mahaoran1997/vision.github.io/assets/images/Model Base.png

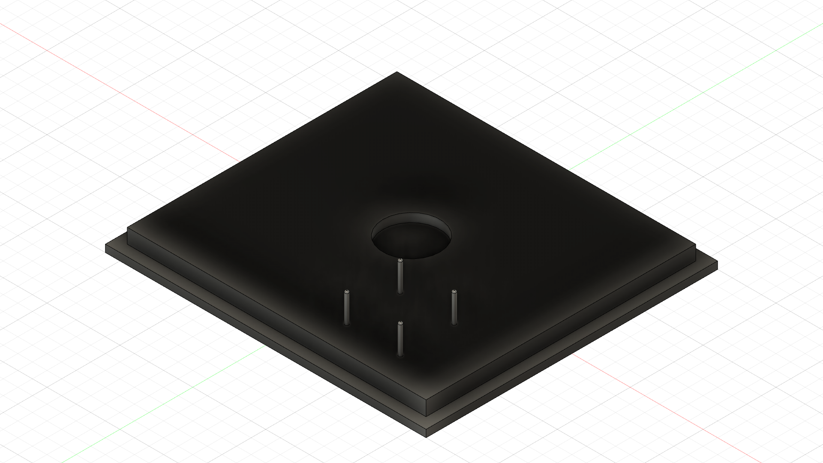
assets/images/Model Base.png
