mahaoran1997/vision.github.io/assets/images/Model Cover.png

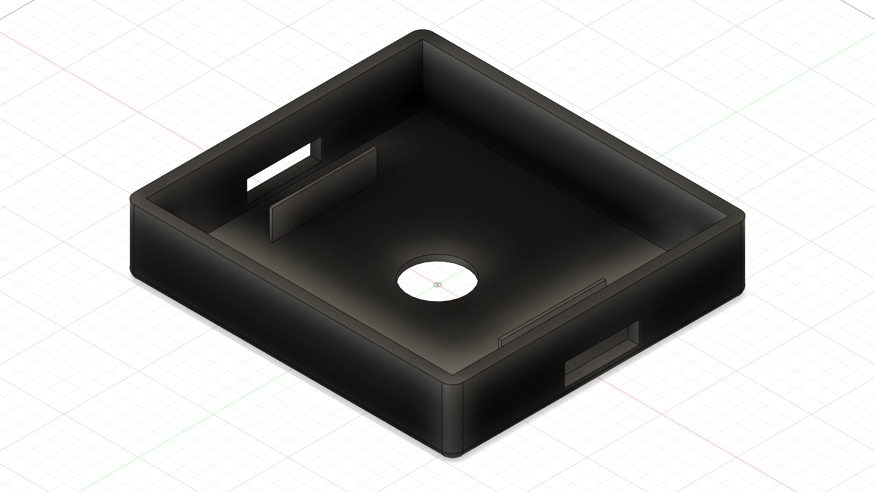
assets/images/Model Cover.png
