mahaoran1997/vision.github.io/assets/images/pattern1_1.JPG

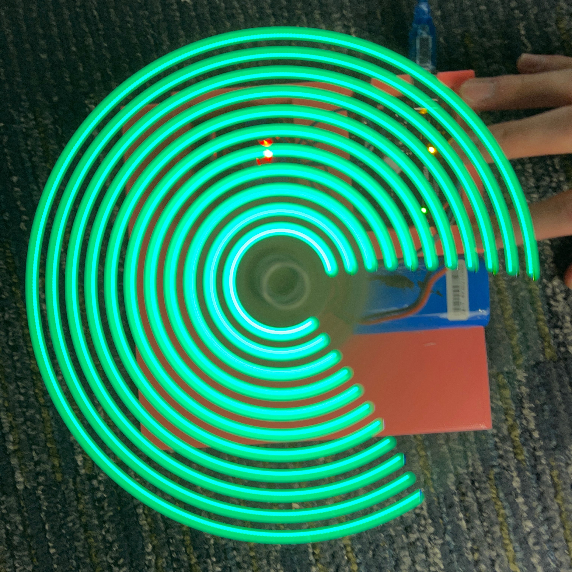
assets/images/pattern1_1.JPG
