mahaoran1997/vision.github.io/assets/images/pattern2_1.JPG

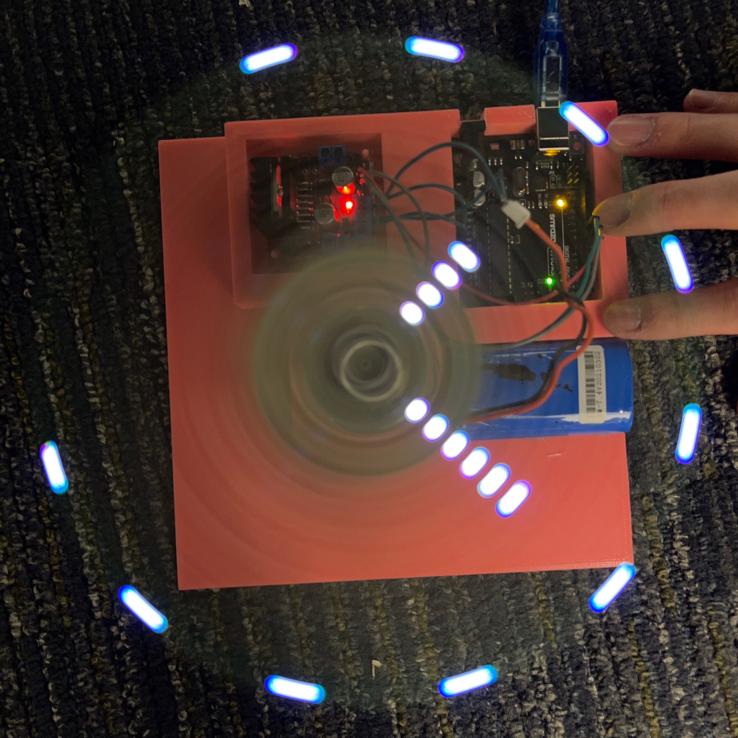
assets/images/pattern2_1.JPG
