mahaoran1997/vision.github.io/assets/images/pattern3_1.JPG

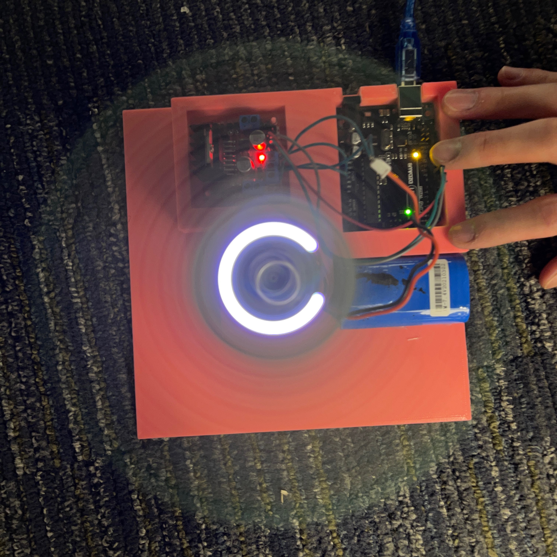
assets/images/pattern3_1.JPG
