mahaoran1997/vision.github.io/assets/images/pattern3_2.JPG

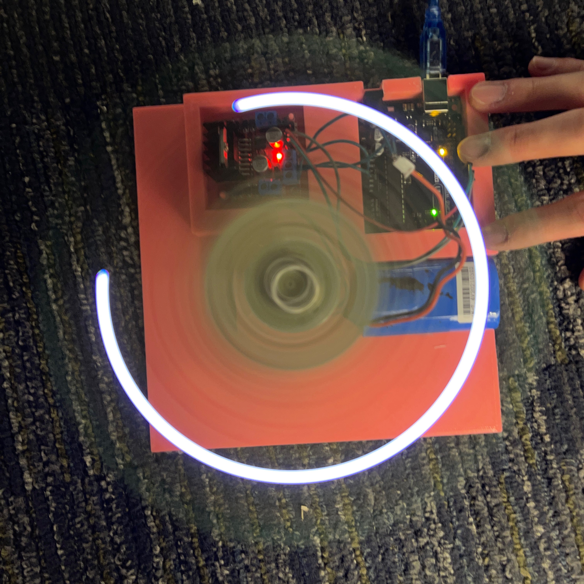
assets/images/pattern3_2.JPG
