mahaoran1997/vision.github.io/assets/images/pattern3_3.JPG

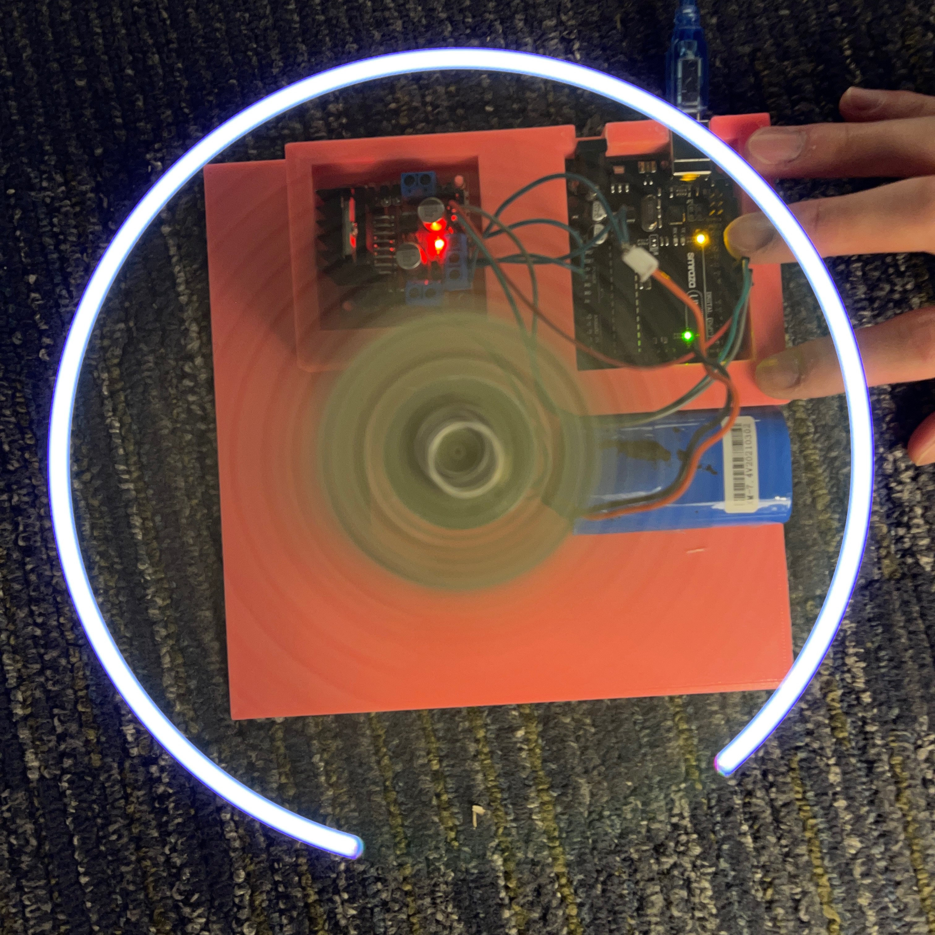
assets/images/pattern3_3.JPG
