mahaoran1997/vision.github.io/assets/images/pattern4.jpg

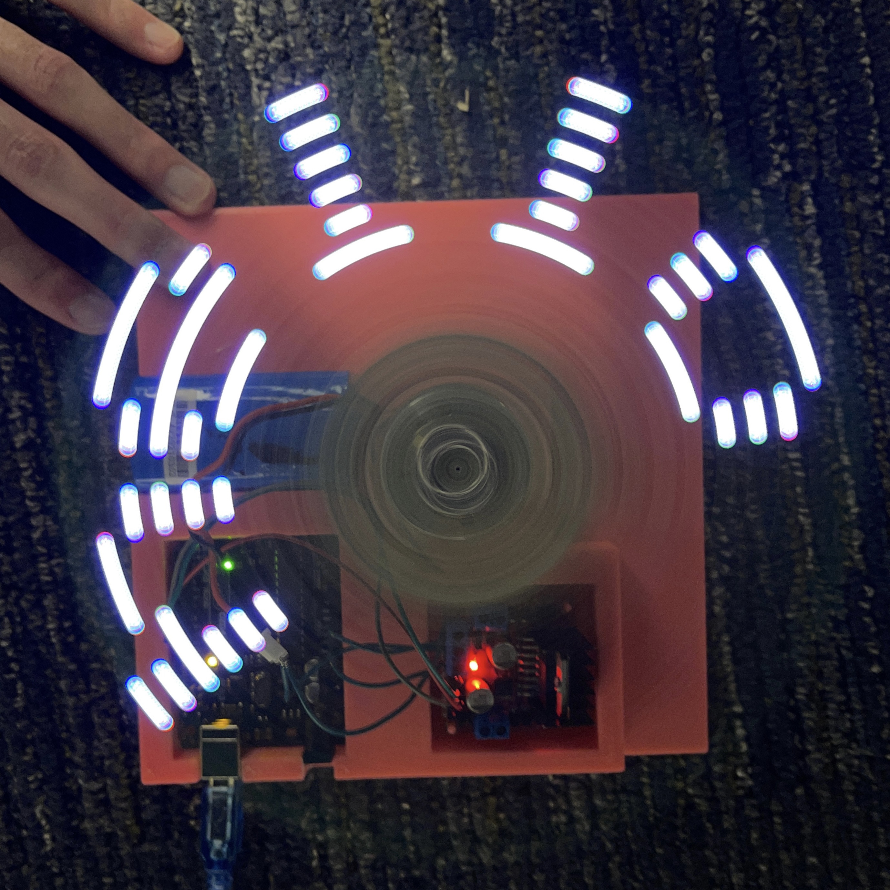
assets/images/pattern4.jpg
